iotdevspot/nikon-lightning-sensing-shutter-remote/images/2.png

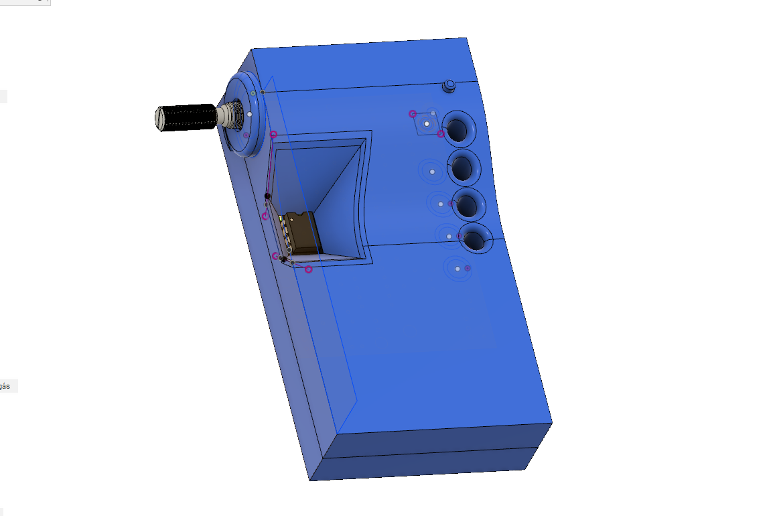
images/2.png
