iotdevspot/nikon-lightning-sensing-shutter-remote/images/5.png

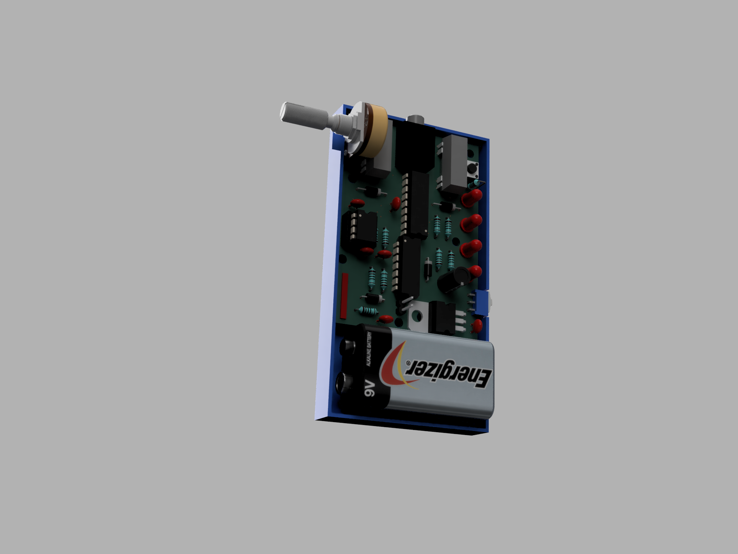
images/5.png
