iotdevspot/nikon-lightning-sensing-shutter-remote/images/6.GIF

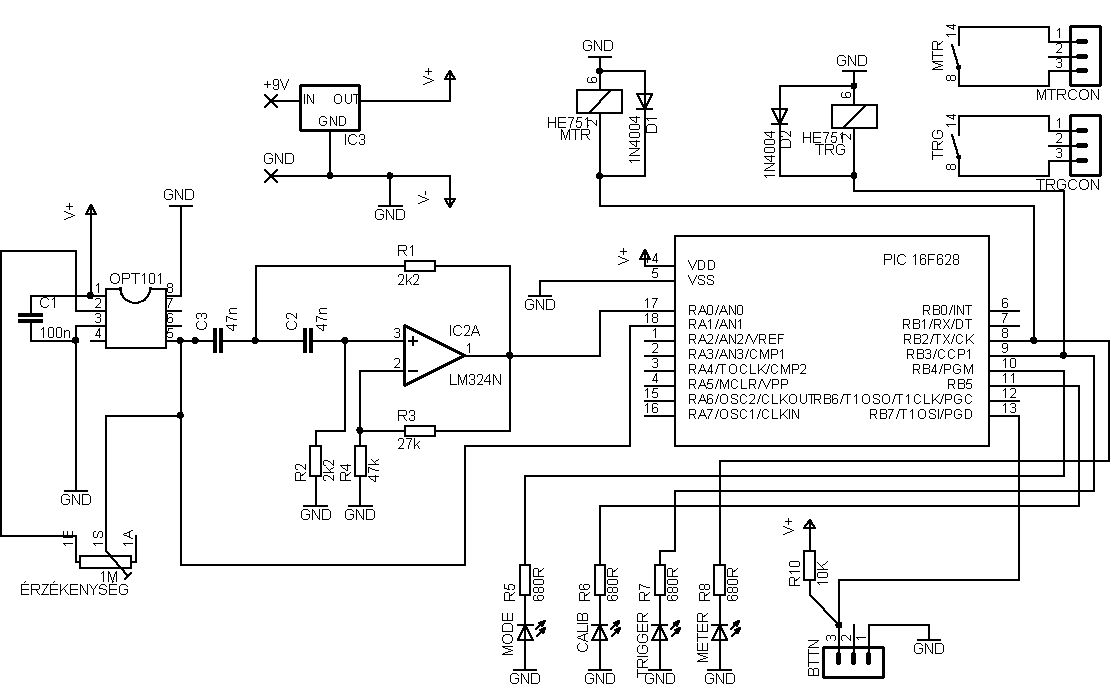
images/6.GIF
